MakersFunDuck/Common-Kitchen-Timer-With-LCD-Replacement-Board/KiCAD files/20231217_142930.jpg

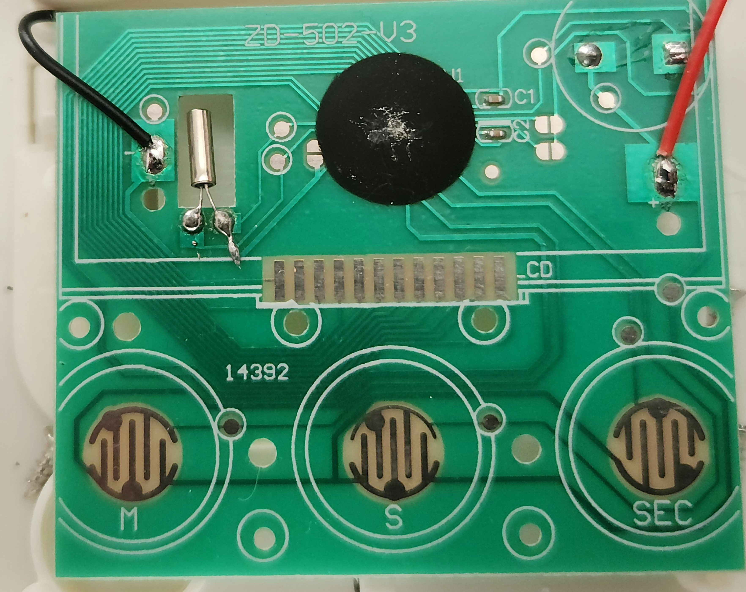
KiCAD files/20231217_142930.jpg
